kareemcru/Smart-Farming-System/20210517_161234.jpg

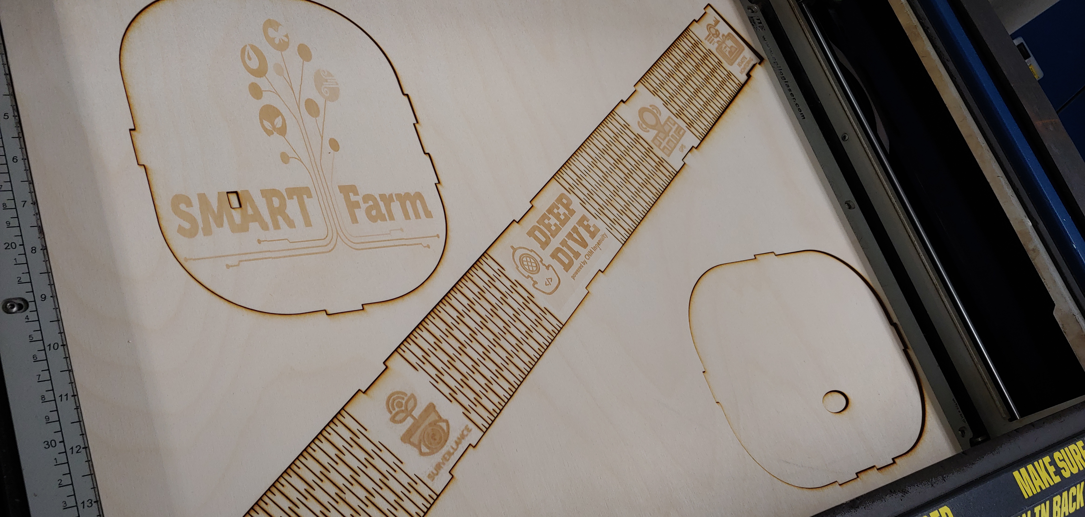
20210517_161234.jpg
