kareemcru/Smart-Farming-System/20210517_161238.jpg

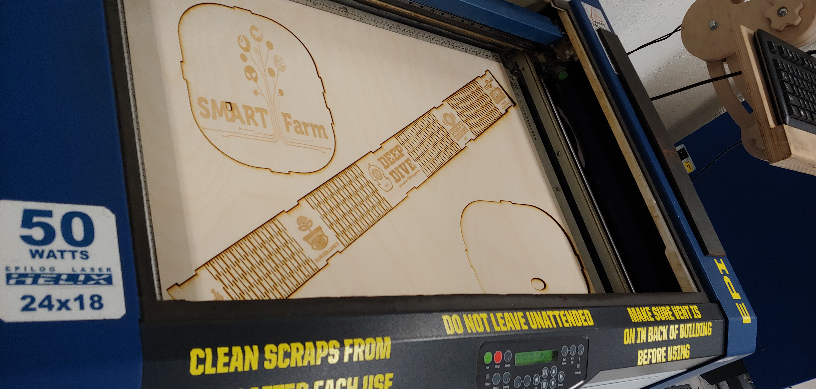
20210517_161238.jpg
