kareemcru/Smart-Farming-System/20210518_083805.jpg

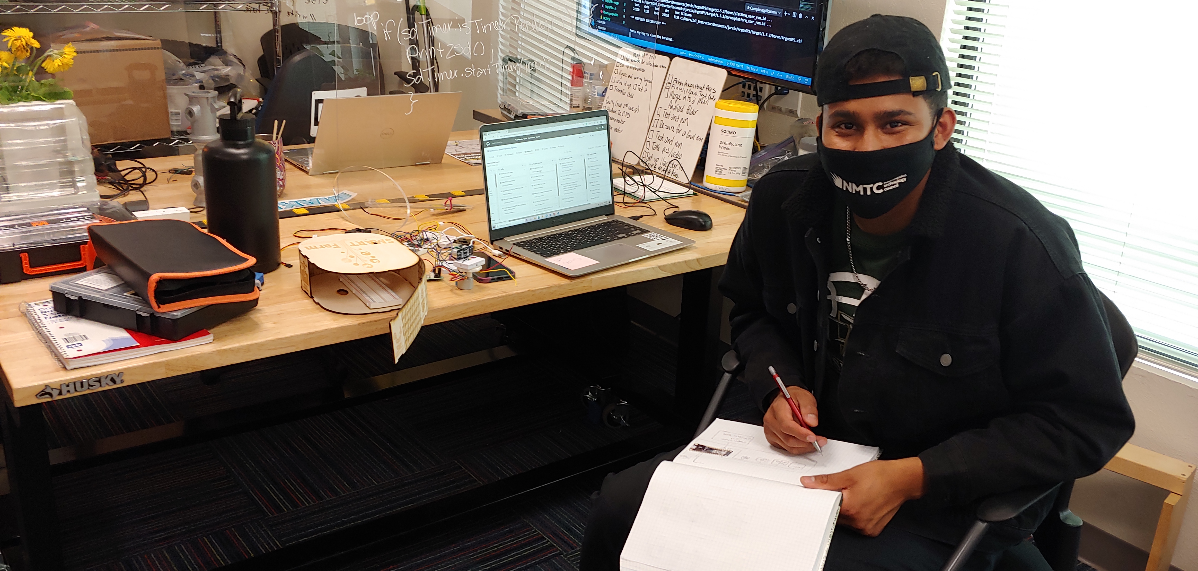
20210518_083805.jpg
