kareemcru/Smart-Farming-System/20210518_172133.jpg

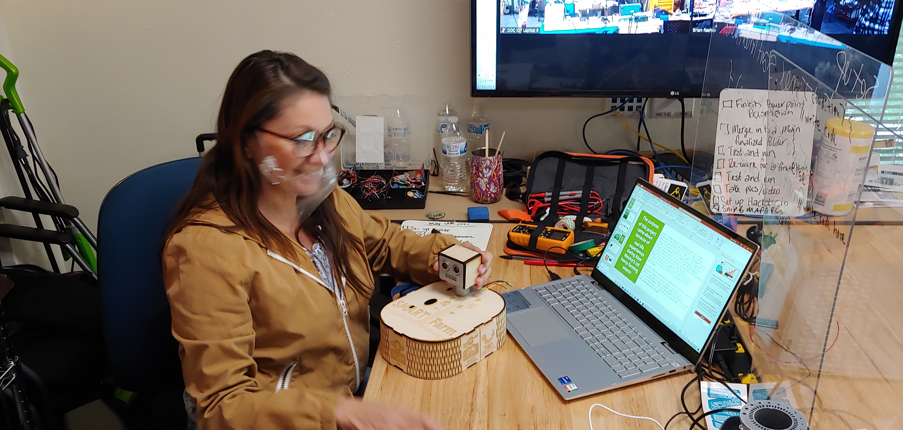
20210518_172133.jpg
